Obijuan/Miniskybot/parts/futaba3003/futaba-doc1.dxf

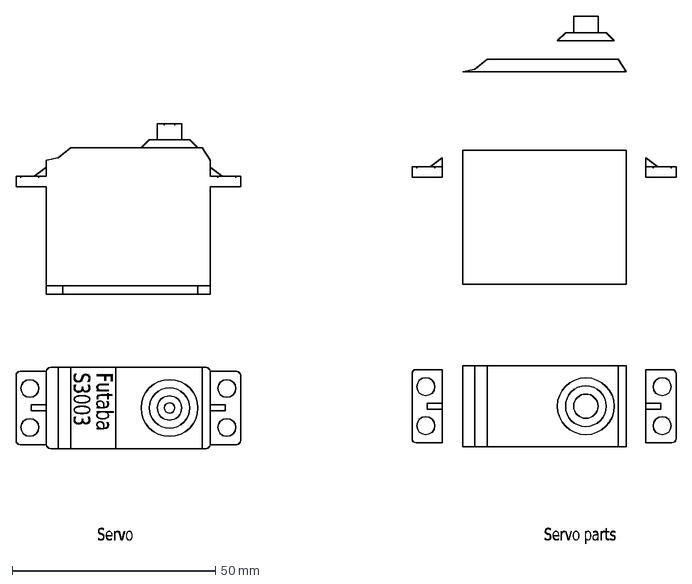
[picture p18: CAD file, 2012-03-20]
parts/futaba3003/futaba-doc1.dxf
Futaba
S3003
Servo
Servo\~parts
