Obijuan/Miniskybot/parts/futaba3003/futaba.stl

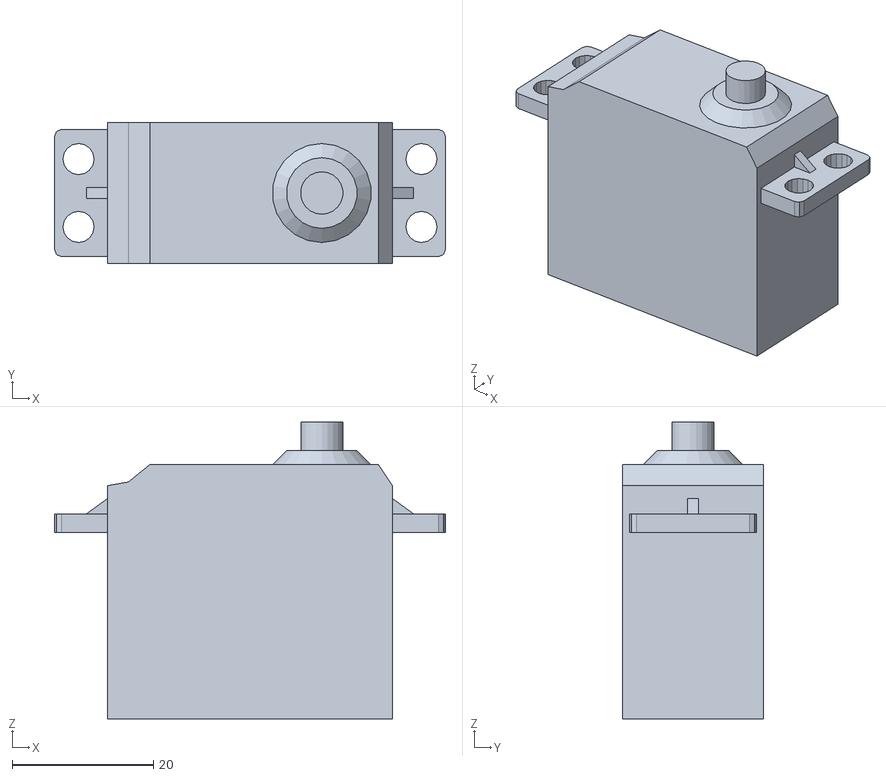
[picture p19: CAD file, 2012-03-20]
parts/futaba3003/futaba.stl
55.3 x 20.0 x 42.0
