Obijuan/Miniskybot/parts/futaba3003/futaba-ears.dxf

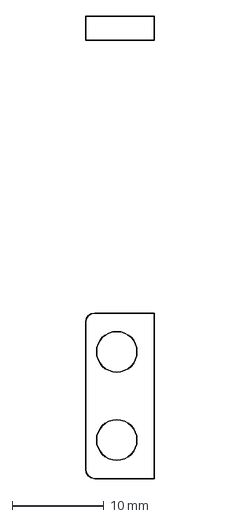
[picture p20: CAD file, 2012-03-20]
parts/futaba3003/futaba-ears.dxf
7.50 x 50.3 mm
