Obijuan/Miniskybot/parts/futaba3003/futaba_plate.scad

module futaba_plate()
{
  dxf_rotate_extrude(file="futaba-plate.dxf", layer="section");
   
}


futaba_plate();
