Obijuan/Miniskybot/parts/Freecad/non-printable/marbel.scad

sphere(r=16/2);
